Egray180/allspark/images/analog_layout.png

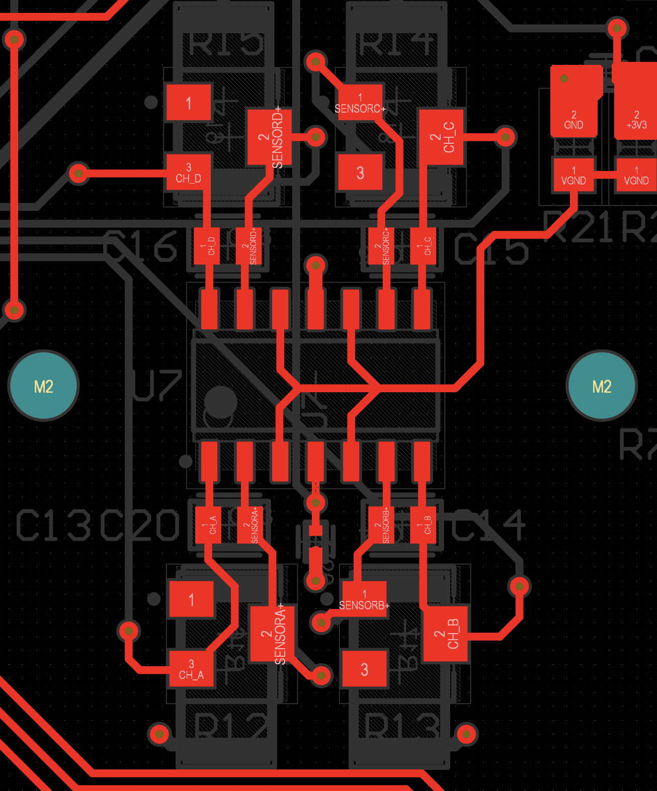
images/analog_layout.png
