Egray180/allspark/images/case2.jpg

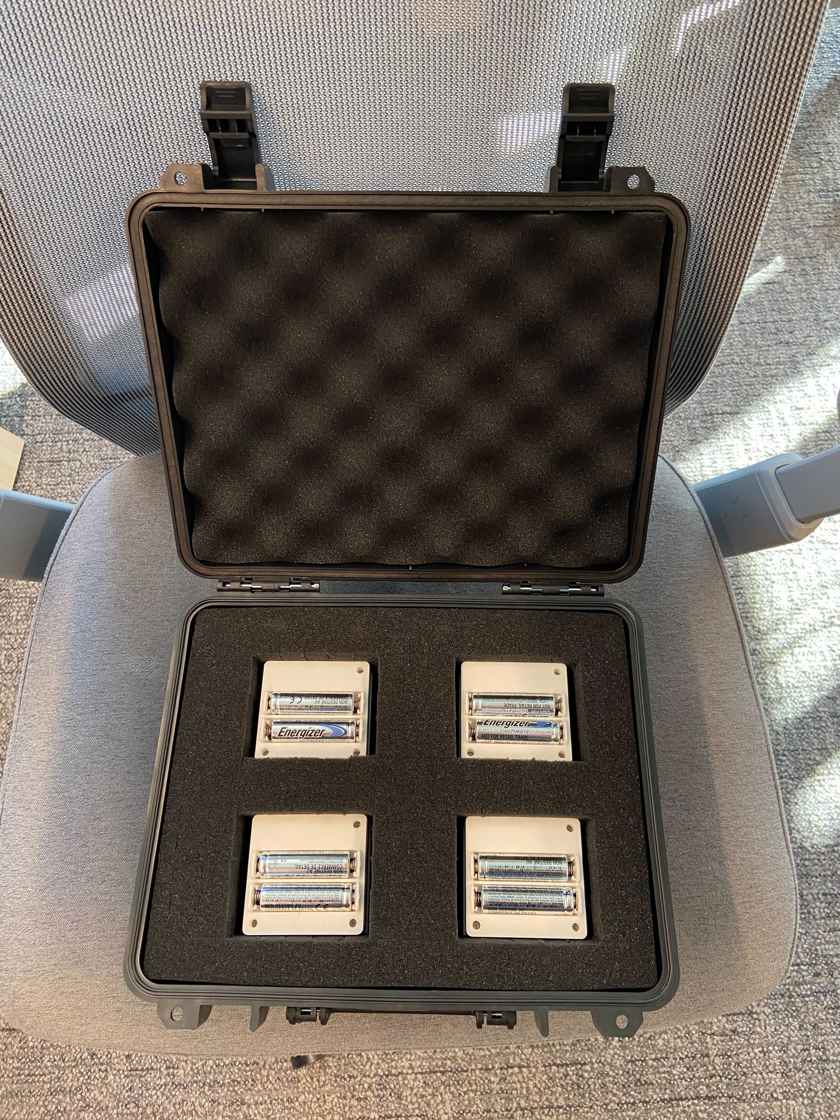
images/case2.jpg
