Egray180/allspark/images/case3.jpg

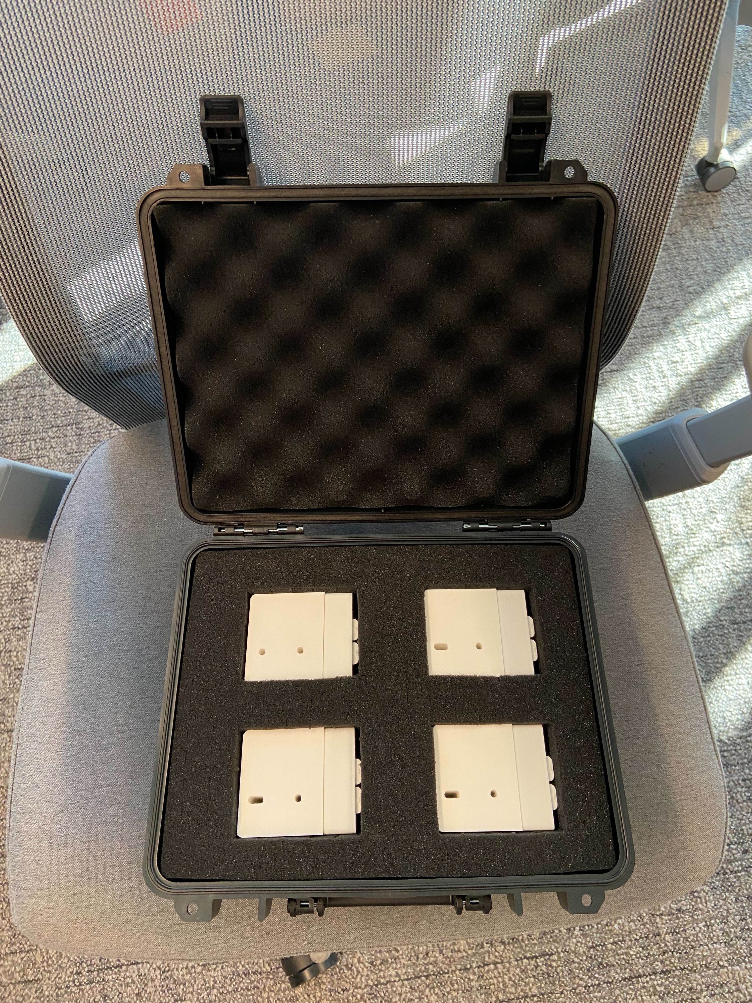
images/case3.jpg
