Egray180/allspark/images/jlc_bot.png

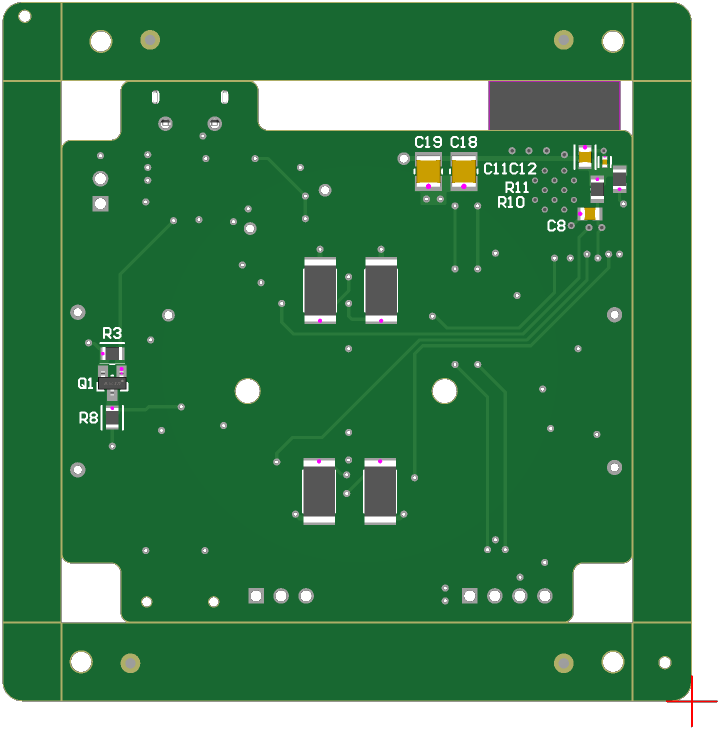
images/jlc_bot.png
