Egray180/allspark/images/jlc_top.png

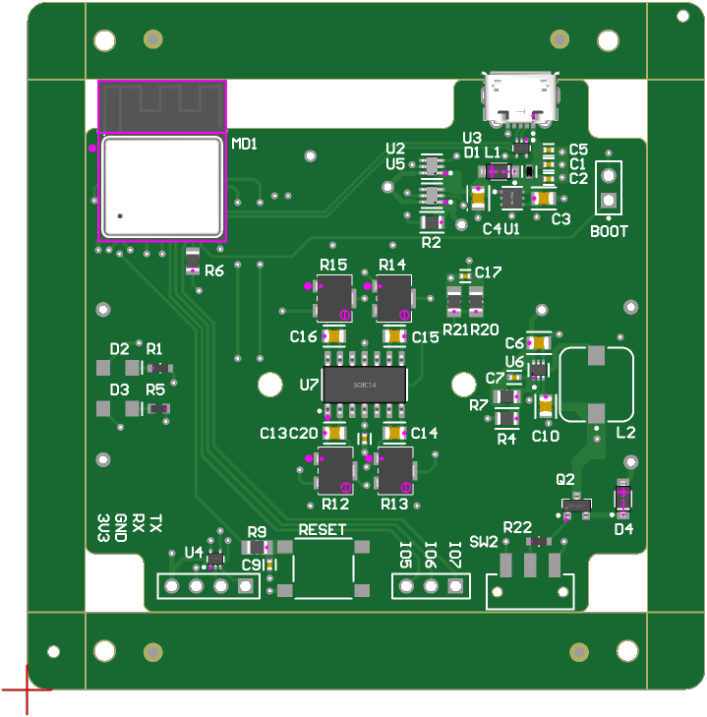
images/jlc_top.png
