Egray180/allspark/images/set2.jpg

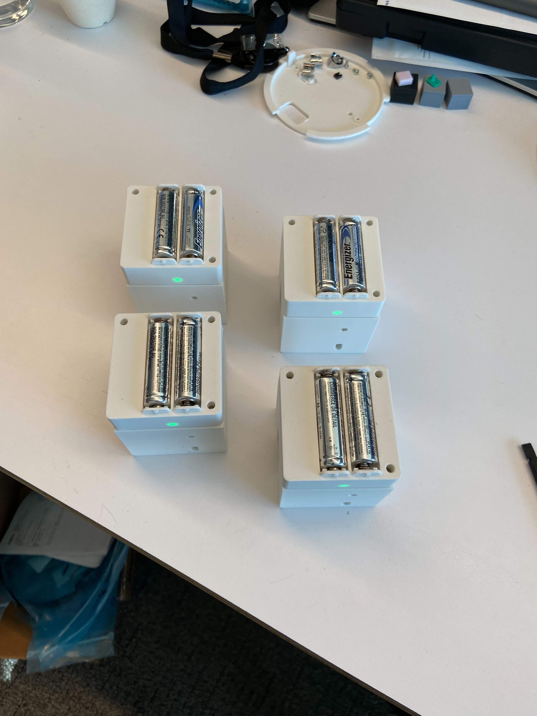
images/set2.jpg
